na103/BigBlue/Images/1.jpg

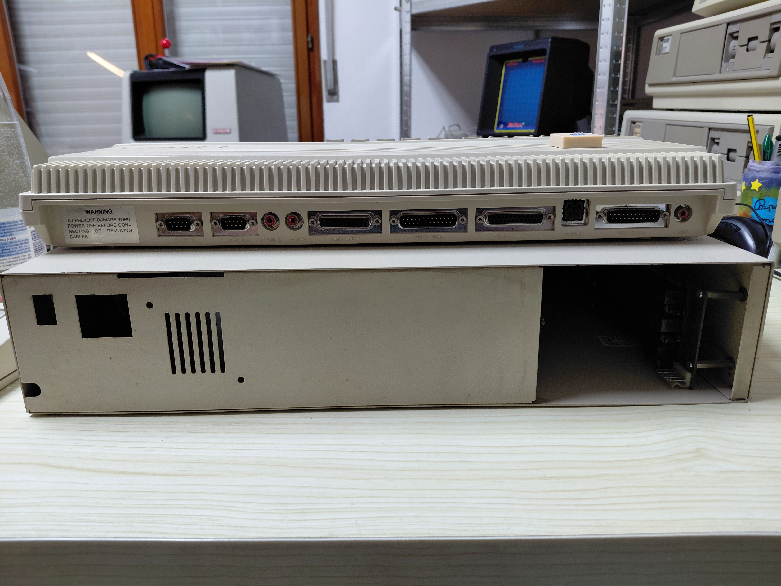
Images/1.jpg
