na103/BigBlue/Images/2.jpg

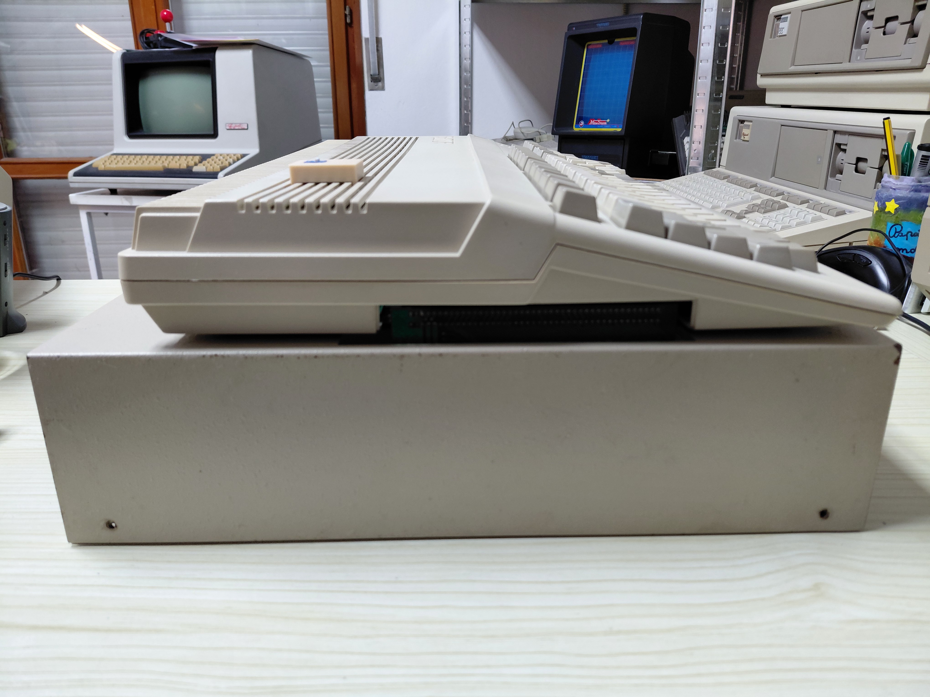
Images/2.jpg
