na103/BigBlue/Images/3.jpg

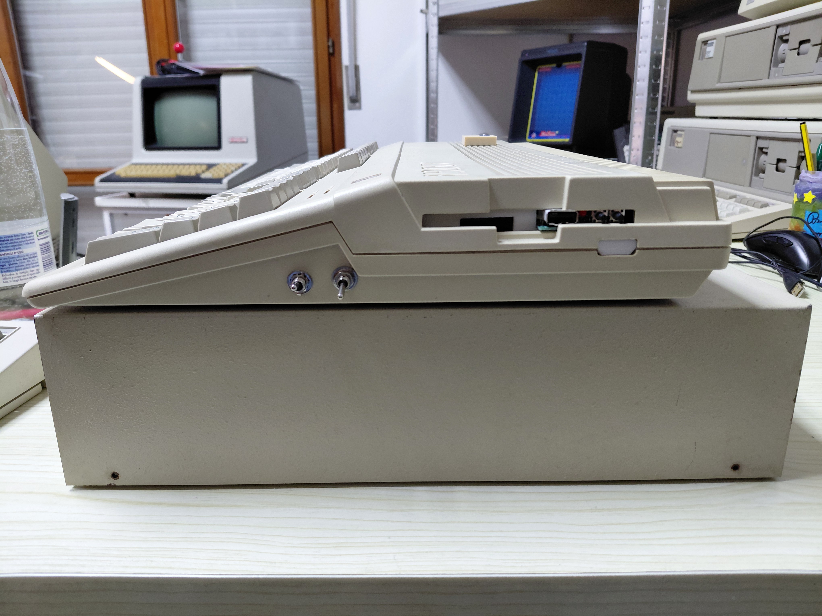
Images/3.jpg
