na103/BigBlue/Images/4.jpg

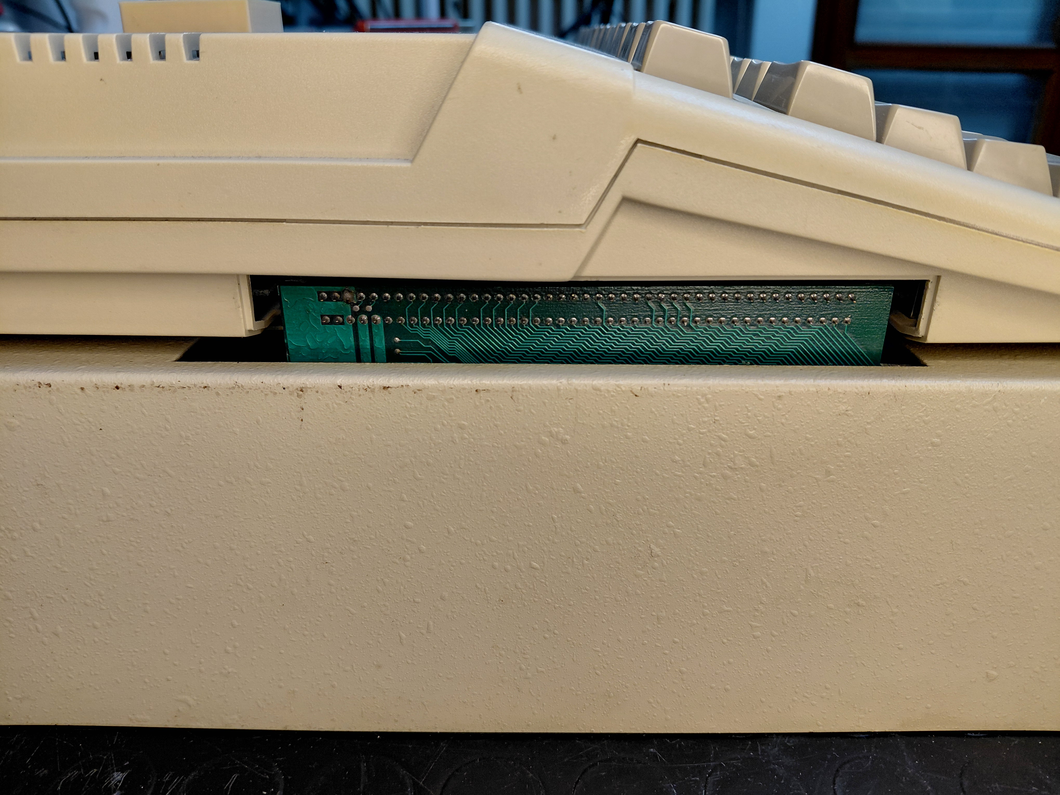
Images/4.jpg
