na103/BigBlue/Images/6.jpg

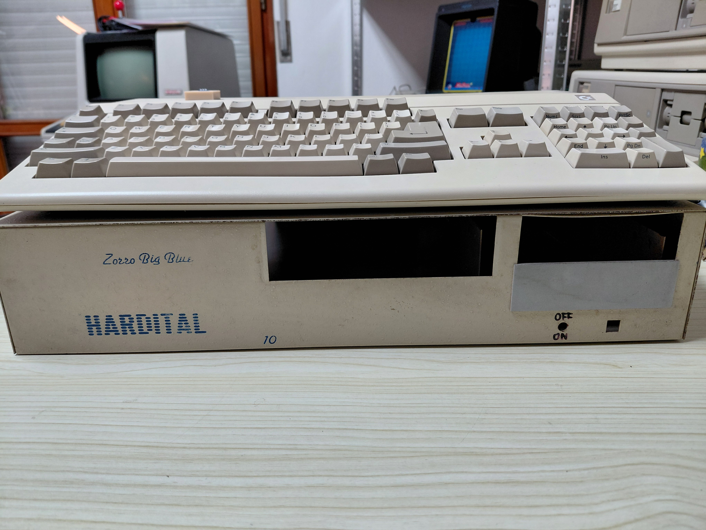
Images/6.jpg
