na103/BigBlue/Misc/ComputerClub1.jpg

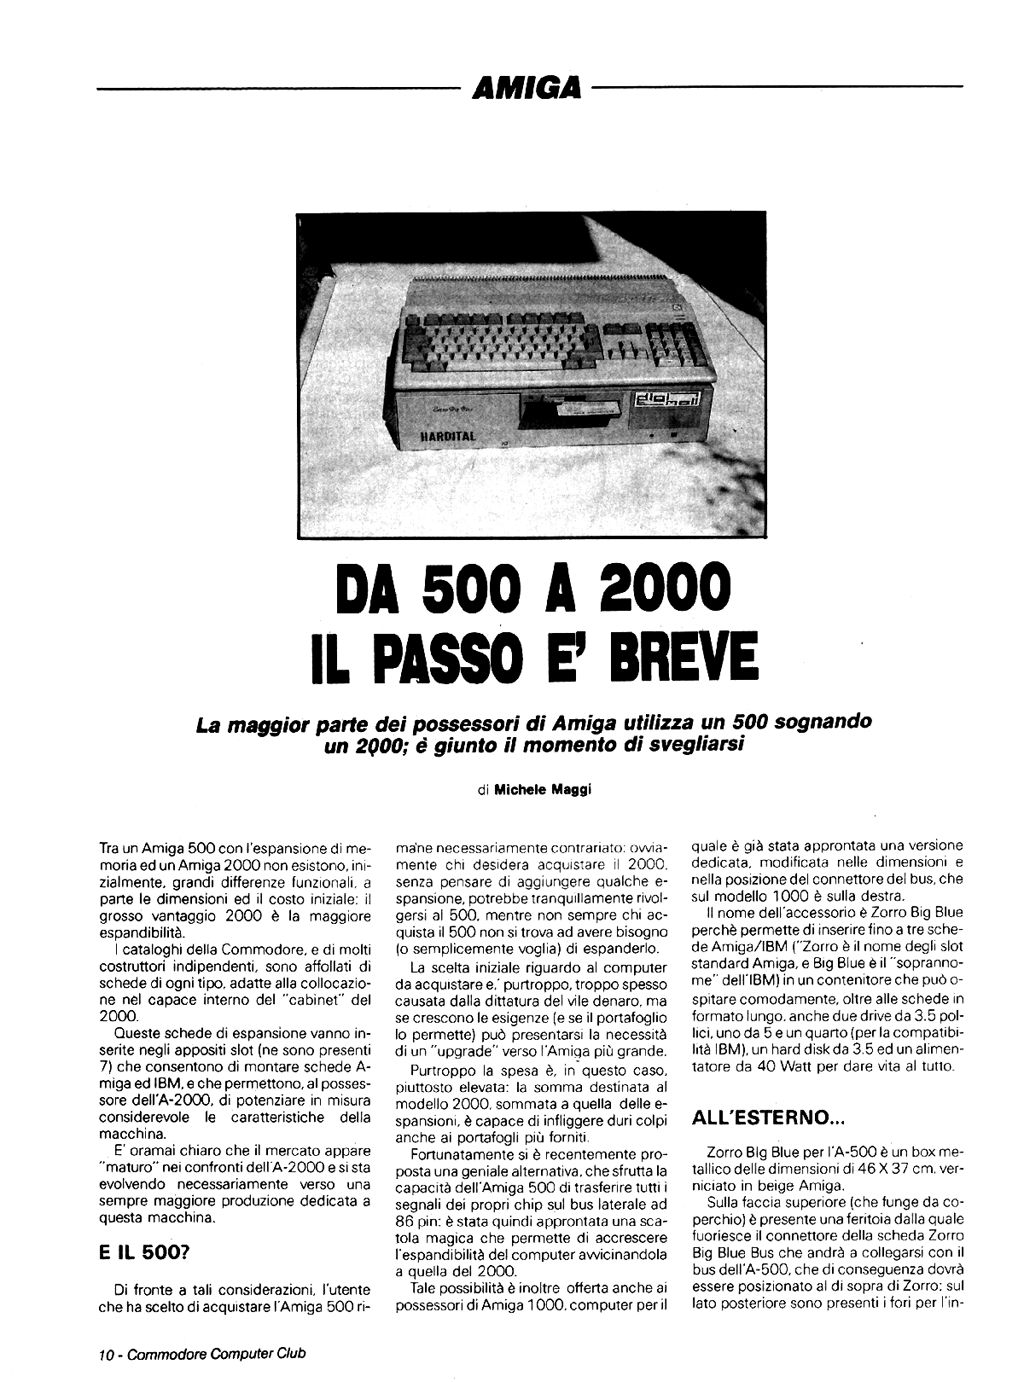
Misc/ComputerClub1.jpg
