na103/BigBlue/Misc/ComputerClub2.jpg

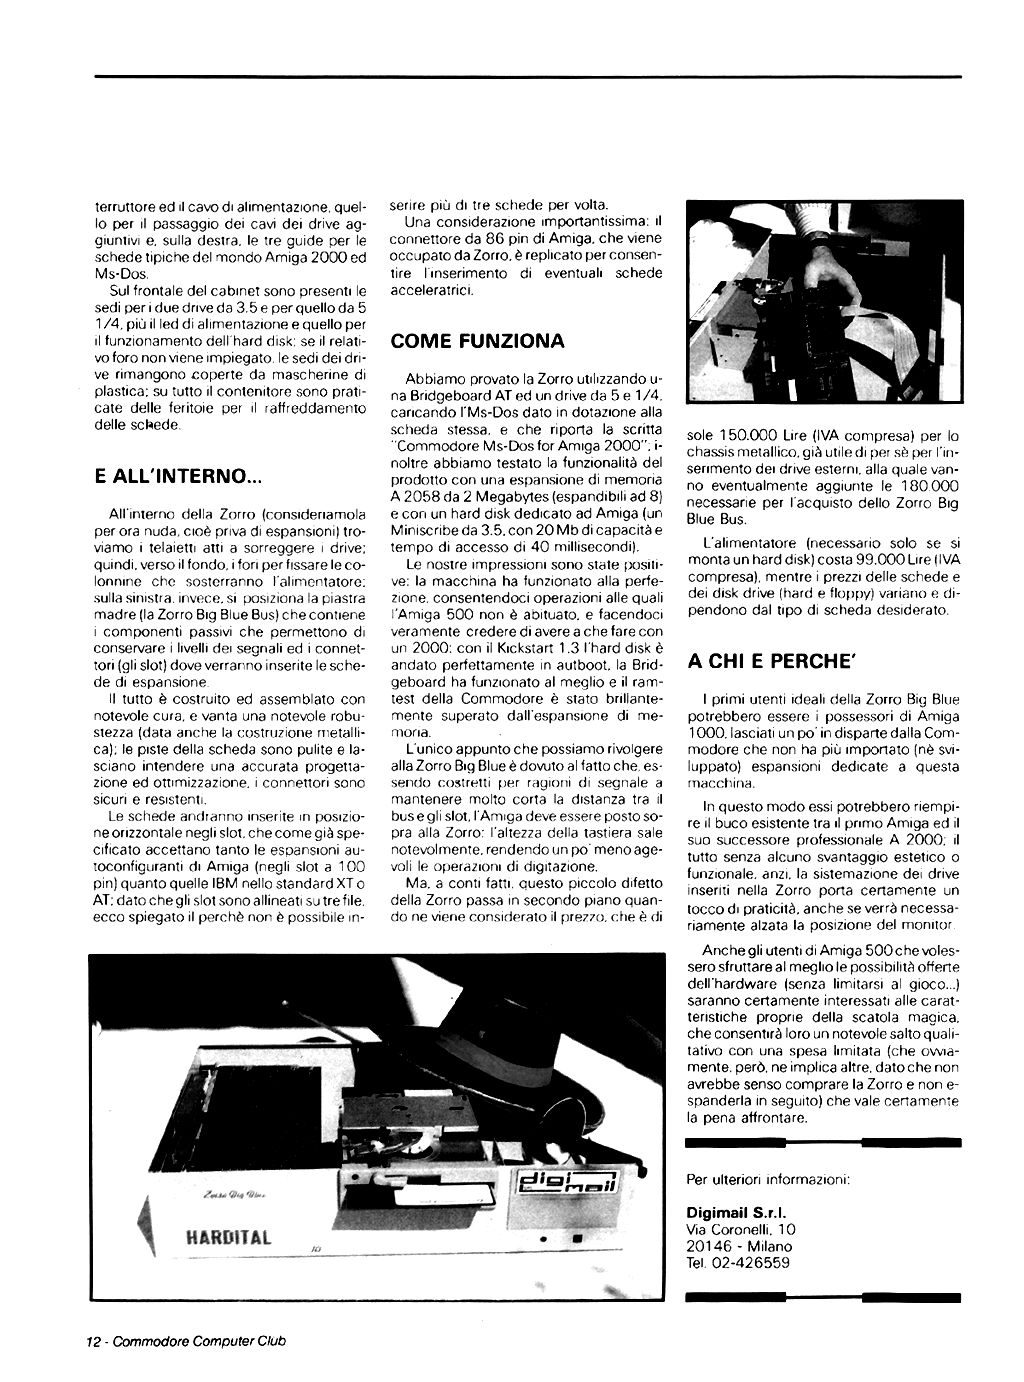
Misc/ComputerClub2.jpg
