na103/BigBlue/Misc/TGM.jpeg

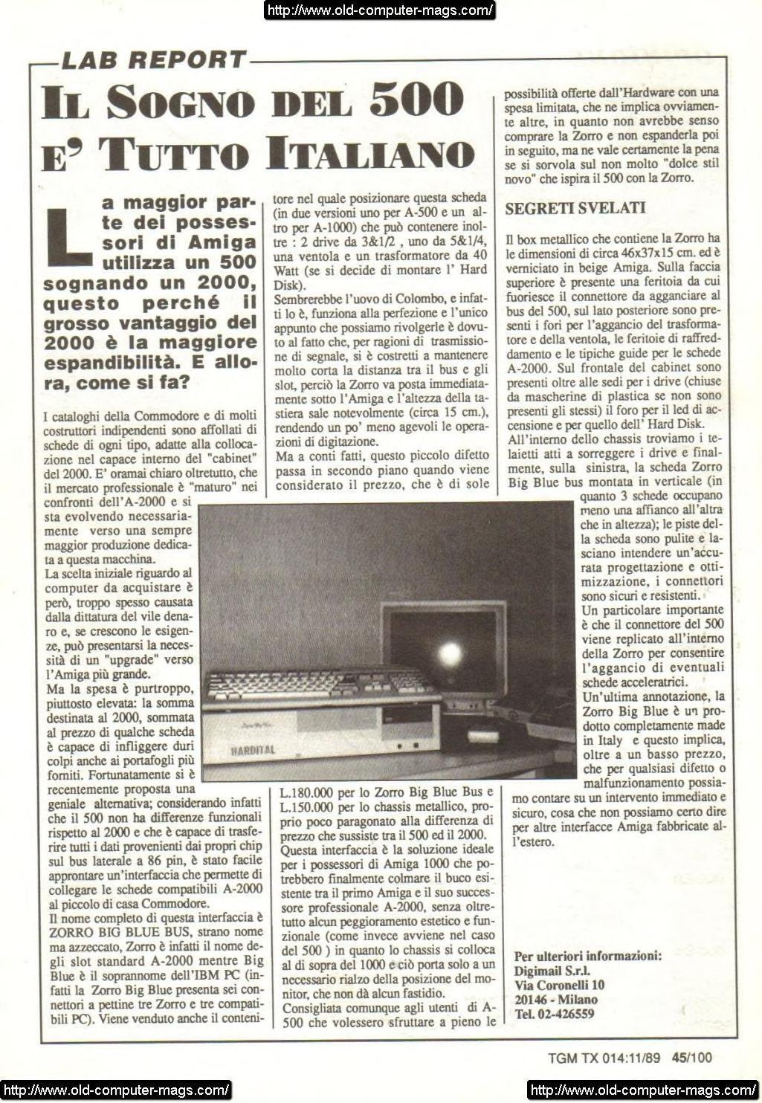
Misc/TGM.jpeg
