na103/BigBlue/PAL/Docs/A2000TRM_044.png

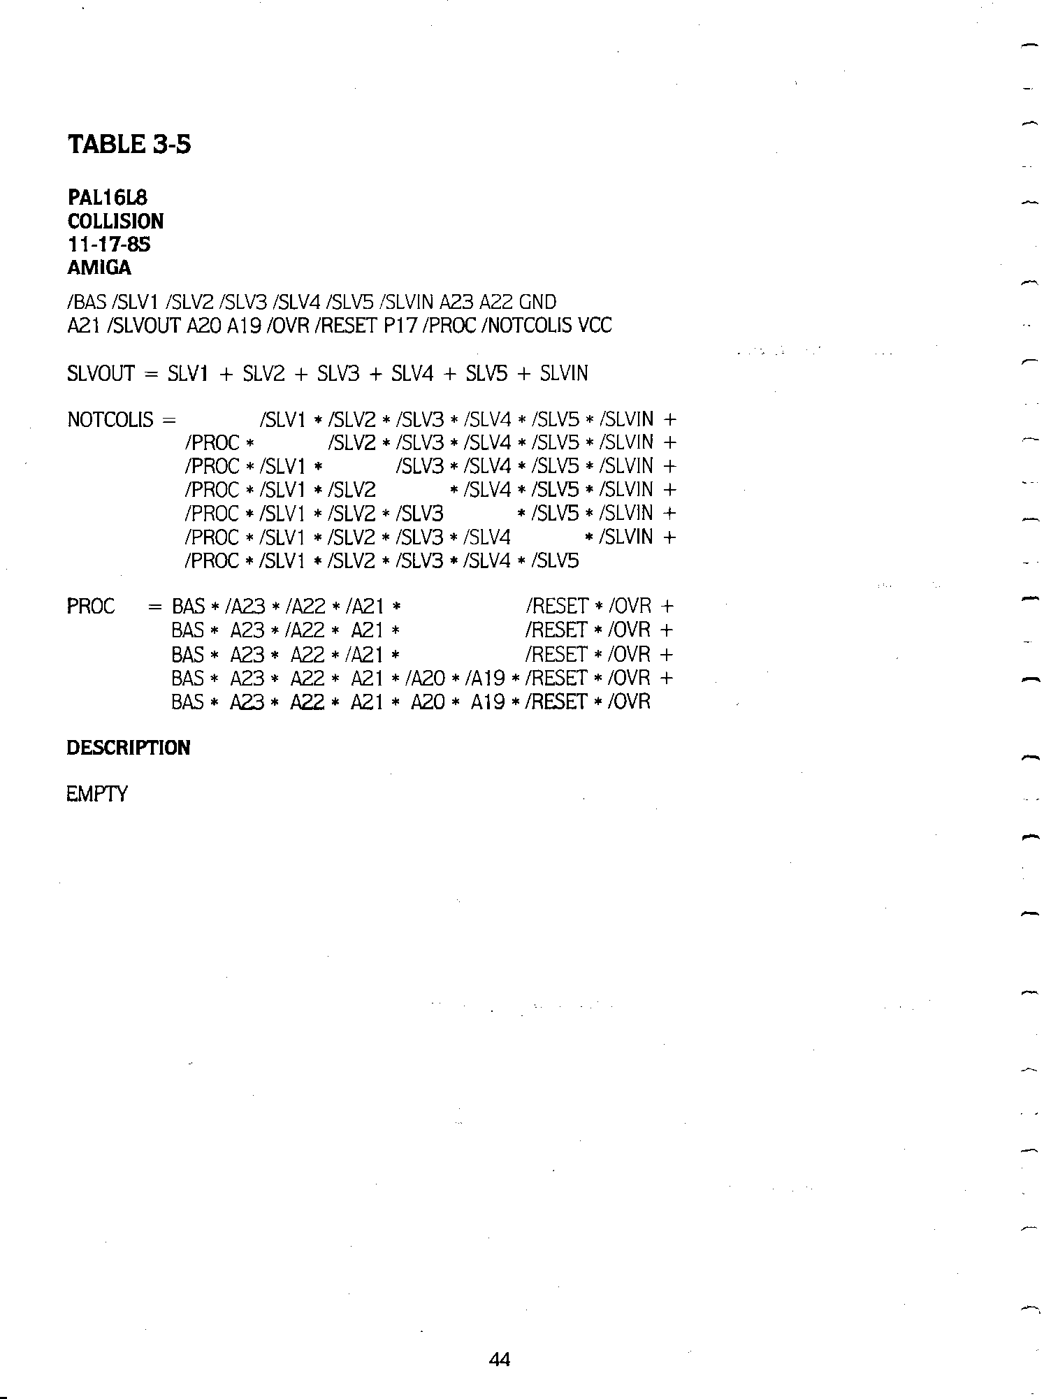
PAL/Docs/A2000TRM_044.png
