na103/BigBlue/PAL/Docs/A2000TRM_A2_a.png

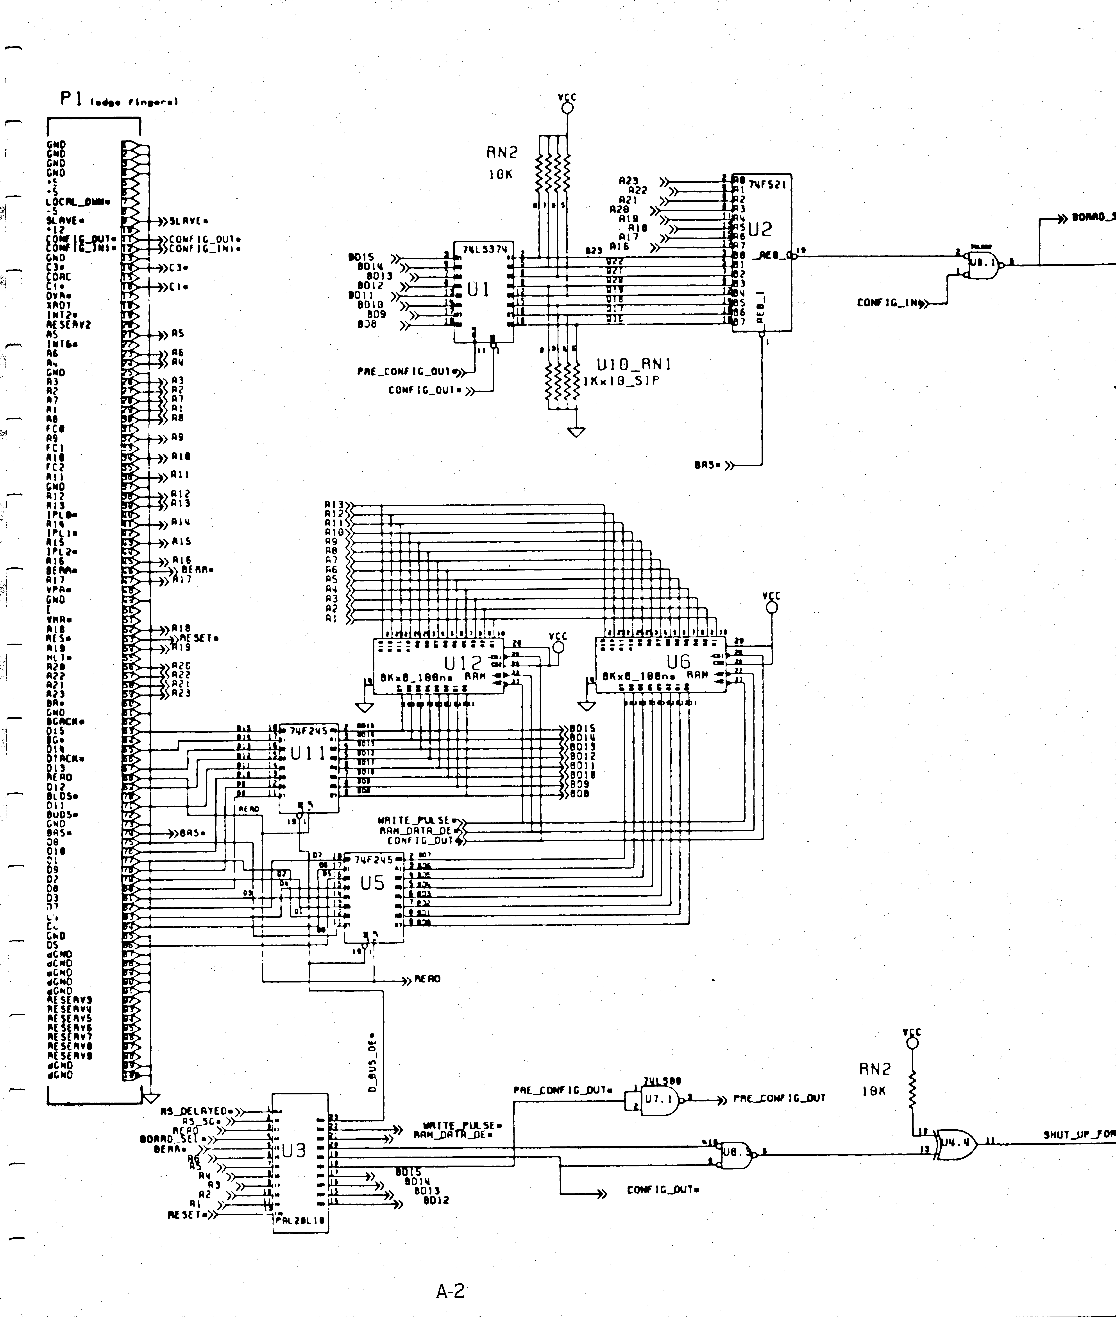
PAL/Docs/A2000TRM_A2_a.png
